sukiyra/sms-forwarder-board/code/globals.h

#ifndef GLOBALS_H
#define GLOBALS_H

#include <Arduino.h>
#include <WiFi.h>
#include <WiFiClientSecure.h>
#include <WebServer.h>
#include <Preferences.h>
#include <pdulib.h>
#define ENABLE_SMTP
#define ENABLE_DEBUG
#include <ReadyMail.h>
#include "config_types.h"

// 串口映射
#define TXD 3
#define RXD 4
#define MODEM_EN_PIN 5

// LED引脚定义（用于通过CI验证，给个假的）
#ifndef LED_BUILTIN
#define LED_BUILTIN 8
#endif

#define SERIAL_BUFFER_SIZE 500
#define MODEM_RX_BUFFER_SIZE 8192
#define MAX_PDU_LENGTH 300
#define FIRMWARE_VERSION "sukiyra-1.6.5"

// 全局变量声明
extern Config config;
extern Preferences preferences;
extern PDU pdu;
extern WiFiClientSecure ssl_client;
extern SMTPClient smtp;
extern WebServer server;
extern bool configValid;
extern bool modemReady;
extern String detectedModemManufacturer;
extern String detectedModemModel;
extern String detectedModemFirmware;
extern String detectedModemFamily;
extern unsigned long lastPrintTime;
extern ConcatSms concatBuffer[MAX_CONCAT_MESSAGES];

#endif
