sukiyra/sms-forwarder-board/code/web_handlers.h

#ifndef WEB_HANDLERS_H
#define WEB_HANDLERS_H

#include "globals.h"

#define LOG_BUF_SIZE 80
#define LOG_LINE_MAX_SIZE 320

extern String logBuffer[LOG_BUF_SIZE];
extern int logBufIdx;
extern int logBufCount;

void logCapture(const String& msg);
void logCapture(const char* msg);
void logCaptureF(const char* fmt, ...);
void logCaptureLn(const String& msg);
void logCaptureLn(const char* msg);

bool checkAuth();
void sendJsonResponse(int status, const String &json);
void handleRoot();
void handleQuery();
bool wifiConnectAll();
void wifiStartAp();
void wifiMaintenanceLoop();
bool wifiProvisioningMode();
bool wifiStartScan(String &message);
String wifiScanStatusJson();
bool wifiStartConnectionTest(const String &ssid, const String &pass, String &message);
String wifiConnectionTestJson();
void handleATCommand();
void handlePing();
void handleLog();
void handleModem();
void handleWifi();

#endif
