sukiyra/sms-forwarder-board/code/push.h

#ifndef PUSH_H
#define PUSH_H

#include "globals.h"

void sendEmailNotification(const char* subject, const char* body);
void sendSMSToServer(const char* sender, const char* message, const char* timestamp);
void sendToChannel(const PushChannel& channel, const char* sender, const char* message, const char* timestamp);
String urlEncode(const String& str);
String jsonEscape(const String& str);
String notificationDisplayTime(const char* timestamp);
String dingtalkSign(const String& secret, int64_t timestamp);
int64_t getUtcMillis();

#endif
