sukiyra/sms-forwarder-board/code/sim_manager.cpp

#include "sim_manager.h"

#include "esim_manager.h"
#include "globals.h"
#include "modem.h"
#include "operator_manager.h"
#include "sms_process.h"
#include "sim_policy.h"
#include "web_handlers.h"

namespace {

constexpr unsigned long DETECT_INTERVAL_READY_MS = 2000UL;
constexpr unsigned long DETECT_INTERVAL_RETRY_MS = 1000UL;
constexpr unsigned long DETECT_CONFIRM_MS = 350UL;
constexpr unsigned long ML307Y_ABSENT_CONFIRM_MS = 3000UL;
constexpr unsigned long COMMAND_TIMEOUT_MS = 2500UL;
constexpr unsigned long CGACT_TIMEOUT_MS = 5000UL;
constexpr unsigned long SIGNAL_INTERVAL_MS = 10000UL;
constexpr unsigned long SIGNAL_STALE_MS = 45000UL;
constexpr size_t RESPONSE_CAPACITY = 640;
constexpr uint8_t CONFIRMATION_COUNT = 2;

enum SimState {
  SIM_UNKNOWN,
  SIM_DETECTING,
  SIM_ABSENT,
  SIM_PIN_REQUIRED,
  SIM_PUK_REQUIRED,
  SIM_READY,
  SIM_ERROR
};

enum Observation {
  OBS_UNKNOWN,
  OBS_DETECTING,
  OBS_ABSENT,
  OBS_PIN_REQUIRED,
  OBS_PUK_REQUIRED,
  OBS_READY,
  OBS_ERROR
};

enum WireStage {
  WIRE_IDLE,
  WIRE_CPIN,
  WIRE_CMEE,
  WIRE_CGACT,
  WIRE_ICCID,
  WIRE_ICCID_CRSM,
  WIRE_CNUM,
  WIRE_CIMI,
  WIRE_CNMI,
  WIRE_CNMI_STORED,
  WIRE_CMGF,
  WIRE_CEREG_ENABLE,
  WIRE_CEREG_QUERY,
  WIRE_CEREG_PROBE,
  WIRE_CEREG_SIM_VERIFY,
  WIRE_CESQ
};

SimState state = SIM_UNKNOWN;
Observation candidate = OBS_UNKNOWN;
uint8_t candidateCount = 0;
WireStage wireStage = WIRE_IDLE;
bool known = false;
bool present = false;
bool smsReady = false;
bool needsConfigure = false;
bool ownsExclusive = false;
bool probeRegistrationNext = false;
uint8_t configAttempts = 0;
uint8_t transportFailures = 0;
uint8_t ml307yAbsentVerificationFailures = 0;
uint32_t generation = 0;
unsigned long changedAt = 0;
unsigned long nextActionAt = 0;
unsigned long commandStartedAt = 0;
unsigned long commandTimeout = COMMAND_TIMEOUT_MS;
char responseBuffer[RESPONSE_CAPACITY];
size_t responseLength = 0;
String activeIccidTail;
String activePhoneNumber;
String activeHomePlmn;
int activeRegistrationStatus = -1;
bool signalKnown = false;
bool signalRsrqKnown = false;
int signalRsrpDbm = 0;
int signalRsrqTenthsDb = 0;
bool startWire(const char* command, WireStage stage,
               unsigned long timeout = COMMAND_TIMEOUT_MS);
int signalRsrpRaw = -1;
int signalRsrqRaw = -1;
unsigned long signalUpdatedAt = 0;
unsigned long signalNextAt = 0;
unsigned long simErrorStartedAt = 0;
unsigned long configurationStartedAt = 0;
String stateDetail;

bool elapsed(unsigned long now, unsigned long deadline) {
  return static_cast<long>(now - deadline) >= 0;
}

const char* stateName(SimState value) {
  switch (value) {
    case SIM_DETECTING: return "detecting";
    case SIM_ABSENT: return "absent";
    case SIM_PIN_REQUIRED: return "pin_required";
    case SIM_PUK_REQUIRED: return "puk_required";
    case SIM_READY: return "ready";
    case SIM_ERROR: return "error";
    default: return "unknown";
  }
}

const char* stateMessage(SimState value) {
  switch (value) {
    case SIM_DETECTING:
      return stateDetail.length()
                 ? stateDetail.c_str()
                 : (present ? "SIM 已识别，正在恢复短信服务" : "正在检测 SIM 卡");
    case SIM_ABSENT: return "未检测到 SIM 卡";
    case SIM_PIN_REQUIRED: return "SIM 卡需要 PIN 解锁";
    case SIM_PUK_REQUIRED: return "SIM 卡需要 PUK 解锁";
    case SIM_READY: return smsReady ? "SIM 已就绪" : "SIM 已识别，短信服务尚未就绪";
    case SIM_ERROR:
      return stateDetail.length() ? stateDetail.c_str() : "SIM 卡持续返回硬件错误";
    default: return "SIM 状态尚未确认";
  }
}

void publishState(SimState next, bool nextKnown, bool nextPresent) {
  bool changed = state != next || known != nextKnown || present != nextPresent;
  state = next;
  known = nextKnown;
  present = nextPresent;
  if (!changed) return;
  ++generation;
  changedAt = millis();
  logCaptureLn(String("SIM 状态更新：") + stateMessage(state));
}

void releaseWire() {
  if (ownsExclusive) modemReleaseExclusive();
  ownsExclusive = false;
  wireStage = WIRE_IDLE;
  responseLength = 0;
  memset(responseBuffer, 0, sizeof(responseBuffer));
}

bool lineEquals(const char* expected) {
  size_t start = 0;
  while (start < responseLength) {
    size_t end = start;
    while (end < responseLength && responseBuffer[end] != '\n') ++end;
    while (start < end && (responseBuffer[start] == '\r' || responseBuffer[start] == ' ')) ++start;
    while (end > start && (responseBuffer[end - 1] == '\r' || responseBuffer[end - 1] == ' ')) --end;
    size_t expectedLength = strlen(expected);
    if (end - start == expectedLength &&
        memcmp(responseBuffer + start, expected, expectedLength) == 0) return true;
    start = end + 1;
  }
  return false;
}

bool responseHas(const char* value) {
  return strstr(responseBuffer, value) != nullptr;
}

bool responseError() {
  return lineEquals("ERROR") || responseHas("+CME ERROR:") || responseHas("+CMS ERROR:");
}

int cmeErrorCode() {
  const char* marker = strstr(responseBuffer, "+CME ERROR:");
  if (!marker) return -1;
  marker += strlen("+CME ERROR:");
  while (*marker == ' ') ++marker;
  if (*marker < '0' || *marker > '9') return -1;
  return atoi(marker);
}

Observation parseCpinObservation() {
  if (responseHas("+CPIN: READY")) return OBS_READY;
  if (responseHas("+CPIN: SIM PIN") || responseHas("SIM PIN required")) return OBS_PIN_REQUIRED;
  if (responseHas("+CPIN: SIM PUK") || responseHas("SIM PUK required")) return OBS_PUK_REQUIRED;
  int cme = cmeErrorCode();
  if (cme == 10 || responseHas("SIM not inserted")) return OBS_ABSENT;
  if (cme == 11) return OBS_PIN_REQUIRED;
  if (cme == 12) return OBS_PUK_REQUIRED;
  if (cme == 14 || cme == 512 || responseHas("SIM busy") || responseHas("SIM not ready")) {
    stateDetail = "SIM / eUICC 正在初始化，设备会自动重试";
    return OBS_DETECTING;
  }
  if (cme == 13 || cme == 15 || responseHas("SIM failure") || responseHas("SIM wrong")) {
    stateDetail = cme >= 0 ? "SIM / eUICC 暂时返回错误 " + String(cme) + "，正在等待恢复"
                           : "SIM / eUICC 暂时返回错误，正在等待恢复";
    return OBS_ERROR;
  }
  // SIM busy/not ready and a missing terminal response are transient. They must
  // never be promoted to a false card-removal event.
  return OBS_UNKNOWN;
}

int parseCeregStatus() {
  int queryStatus = -1;
  int urcStatus = -1;
  const char* search = responseBuffer;
  while (const char* marker = strstr(search, "+CEREG:")) {
    marker += strlen("+CEREG:");
    while (*marker == ' ') ++marker;
    char* end = nullptr;
    long first = strtol(marker, &end, 10);
    if (end != marker && first >= 0 && first <= 5) {
      while (*end == ' ') ++end;
      if (*end != ',') {
        urcStatus = static_cast<int>(first);
      } else {
        const char* secondStart = end + 1;
        while (*secondStart == ' ') ++secondStart;
        // Query responses are <n>,<stat>; extended unsolicited reports are
        // <stat>,"<tac>" and therefore have a quote after the first comma.
        if (*secondStart == '"') {
          urcStatus = static_cast<int>(first);
        } else {
          char* secondEnd = nullptr;
          long second = strtol(secondStart, &secondEnd, 10);
          if (secondEnd != secondStart && second >= 0 && second <= 5) {
            queryStatus = static_cast<int>(second);
          }
        }
      }
    }
    const char* lineEnd = strchr(marker, '\n');
    if (!lineEnd) break;
    search = lineEnd + 1;
  }
  return queryStatus >= 0 ? queryStatus : urcStatus;
}

String parseIccidTail(const char* response) {
  if (!response) return "";
  const char* marker = strstr(response, "+ICCID:");
  if (!marker) return "";
  marker += strlen("+ICCID:");
  const char* lineEnd = marker;
  while (*lineEnd && *lineEnd != '\r' && *lineEnd != '\n') ++lineEnd;
  while (marker < lineEnd && (*marker == ' ' || *marker == '\t')) ++marker;
  while (lineEnd > marker &&
         (lineEnd[-1] == ' ' || lineEnd[-1] == '\t')) --lineEnd;
  if (marker < lineEnd && *marker == '"') ++marker;
  if (lineEnd > marker && lineEnd[-1] == '"') --lineEnd;
  // ML307R may append the ISO/IEC 7816 filler nibble used for an odd-length
  // ICCID (for example 19 decimal digits followed by F).
  if (lineEnd > marker && (lineEnd[-1] == 'F' || lineEnd[-1] == 'f')) --lineEnd;
  const size_t length = static_cast<size_t>(lineEnd - marker);
  if (length < 18 || length > 22) return "";
  for (const char* p = marker; p < lineEnd; ++p) {
    if (!isDigit(*p)) return "";
  }
  String tail;
  tail.reserve(4);
  for (const char* p = lineEnd - 4; p < lineEnd; ++p) tail += *p;
  return tail;
}

String parseCrsmIccidTail(const char* response) {
  if (!response) return "";
  const char* marker = strstr(response, "+CRSM:");
  if (!marker) return "";
  marker = strchr(marker, '"');
  if (!marker) return "";
  ++marker;
  const char* end = strchr(marker, '"');
  if (!end || end - marker != 20) return "";

  String digits;
  digits.reserve(20);
  for (const char* p = marker; p < end; p += 2) {
    if (!isHexadecimalDigit(p[0]) || !isHexadecimalDigit(p[1])) return "";
    digits += p[1];
    digits += p[0];
  }
  if (digits.endsWith("F") || digits.endsWith("f")) digits.remove(digits.length() - 1);
  if (digits.length() < 18 || digits.length() > 20) return "";
  for (size_t i = 0; i < digits.length(); ++i) {
    if (!isDigit(digits[i])) return "";
  }
  return digits.substring(digits.length() - 4);
}

String parsePhoneNumber(const char* response) {
  if (!response) return "";
  const char* marker = strstr(response, "+CNUM:");
  if (!marker) return "";
  marker = strchr(marker, ',');
  if (!marker) return "";
  ++marker;
  while (*marker == ' ' || *marker == '\t') ++marker;

  const char* end = marker;
  if (*marker == '"') {
    ++marker;
    end = strchr(marker, '"');
  } else {
    while (*end && *end != ',' && *end != '\r' && *end != '\n') ++end;
  }
  if (!end || end <= marker) return "";

  String number;
  number.reserve(static_cast<size_t>(end - marker));
  for (const char* p = marker; p < end; ++p) {
    if (*p == '+' && p == marker) {
      number += *p;
    } else if (isDigit(*p)) {
      number += *p;
    } else if (*p != ' ' && *p != '-') {
      return "";
    }
  }
  size_t digits = number.startsWith("+") ? number.length() - 1 : number.length();
  return digits >= 3 && digits <= 20 ? number : "";
}

String parseHomePlmn(const char* response) {
  if (!response) return "";
  const char* line = response;
  while (*line) {
    while (*line == '\r' || *line == '\n' || *line == ' ' || *line == '\t') ++line;
    const char* end = line;
    while (*end && *end != '\r' && *end != '\n') ++end;
    const size_t length = static_cast<size_t>(end - line);
    if (length >= 14 && length <= 16) {
      bool allDigits = true;
      for (const char* p = line; p < end; ++p) {
        if (!isDigit(*p)) {
          allDigits = false;
          break;
        }
      }
      if (allDigits) {
        String plmn;
        plmn.reserve(5);
        for (uint8_t i = 0; i < 5; ++i) plmn += line[i];
        return plmn;
      }
    }
    line = end;
  }
  return "";
}

void clearSignalCache() {
  signalKnown = false;
  signalRsrqKnown = false;
  signalRsrpDbm = 0;
  signalRsrqTenthsDb = 0;
  signalRsrpRaw = -1;
  signalRsrqRaw = -1;
  signalUpdatedAt = 0;
  signalNextAt = millis();
}

bool updateSignalFromCesq() {
  const char* marker = strstr(responseBuffer, "+CESQ:");
  if (!marker) return false;
  int rxlev = 0;
  int ber = 0;
  int rscp = 0;
  int ecno = 0;
  int rsrq = 0;
  int rsrp = 0;
  if (sscanf(marker, "+CESQ: %d,%d,%d,%d,%d,%d",
             &rxlev, &ber, &rscp, &ecno, &rsrq, &rsrp) != 6) {
    return false;
  }

  signalRsrpRaw = rsrp;
  signalRsrqRaw = rsrq;
  signalKnown = rsrp >= 0 && rsrp <= 97;
  signalRsrqKnown = rsrq >= 0 && rsrq <= 34;
  if (signalKnown) signalRsrpDbm = -140 + rsrp;
  if (signalRsrqKnown) signalRsrqTenthsDb = -195 + rsrq * 5;
  signalUpdatedAt = millis();
  return true;
}

void invalidateCardCaches() {
  modemReady = false;
  smsReady = false;
  modemSetSmsDeliveryMode("unconfigured");
  probeRegistrationNext = false;
  activeIccidTail = "";
  activePhoneNumber = "";
  activeHomePlmn = "";
  activeRegistrationStatus = -1;
  clearSignalCache();
  esimManagerResetCapability();
  operatorManagerInvalidate();
  smsResetForSimChange();
}

void commitObservation(Observation observation) {
  candidate = OBS_UNKNOWN;
  candidateCount = 0;
  transportFailures = 0;

  switch (observation) {
    case OBS_DETECTING:
      needsConfigure = false;
      configAttempts = 0;
      modemReady = false;
      smsReady = false;
      publishState(SIM_DETECTING, true, true);
      nextActionAt = millis() + DETECT_INTERVAL_RETRY_MS;
      break;
    case OBS_ABSENT:
      stateDetail = "";
      needsConfigure = false;
      configAttempts = 0;
      if (state != SIM_ABSENT || present) invalidateCardCaches();
      publishState(SIM_ABSENT, true, false);
      nextActionAt = millis() + DETECT_INTERVAL_RETRY_MS;
      break;
    case OBS_PIN_REQUIRED:
      stateDetail = "";
      needsConfigure = false;
      configAttempts = 0;
      if (state != SIM_PIN_REQUIRED || !present) invalidateCardCaches();
      publishState(SIM_PIN_REQUIRED, true, true);
      nextActionAt = millis() + DETECT_INTERVAL_RETRY_MS;
      break;
    case OBS_PUK_REQUIRED:
      stateDetail = "";
      needsConfigure = false;
      configAttempts = 0;
      if (state != SIM_PUK_REQUIRED || !present) invalidateCardCaches();
      publishState(SIM_PUK_REQUIRED, true, true);
      nextActionAt = millis() + DETECT_INTERVAL_RETRY_MS;
      break;
    case OBS_ERROR:
      needsConfigure = false;
      configAttempts = 0;
      if (state != SIM_ERROR || !present) invalidateCardCaches();
      publishState(SIM_ERROR, true, true);
      nextActionAt = millis() + DETECT_INTERVAL_RETRY_MS;
      break;
    case OBS_READY: {
      simErrorStartedAt = 0;
      stateDetail = "";
      bool newlyReady = state != SIM_READY || !present || !smsReady;
      if (newlyReady) {
        modemReady = false;
        smsReady = false;
        esimManagerResetCapability();
        operatorManagerInvalidate();
        needsConfigure = true;
        configAttempts = 0;
        configurationStartedAt = millis();
        publishState(SIM_DETECTING, true, true);
        nextActionAt = millis();
      } else {
        nextActionAt = millis() + DETECT_INTERVAL_READY_MS;
      }
      break;
    }
    default:
      nextActionAt = millis() + DETECT_INTERVAL_RETRY_MS;
      break;
  }
}

void observe(Observation observation) {
  if (observation == OBS_ERROR) {
    unsigned long now = millis();
    if (!simErrorStartedAt) simErrorStartedAt = now;
    if (!simpolicy::hardwareErrorIsPersistent(now - simErrorStartedAt)) {
      candidate = OBS_UNKNOWN;
      candidateCount = 0;
      transportFailures = 0;
      if (state != SIM_READY) publishState(SIM_DETECTING, true, true);
      nextActionAt = now + DETECT_INTERVAL_RETRY_MS;
      return;
    }
    stateDetail = "SIM / eUICC 连续 30 秒返回硬件错误，请检查卡片接触或重启模组";
  } else if (observation == OBS_READY || observation == OBS_ABSENT ||
             observation == OBS_PIN_REQUIRED || observation == OBS_PUK_REQUIRED) {
    simErrorStartedAt = 0;
  }
  bool verifyMl307yAbsent = observation == OBS_ABSENT &&
                           detectedModemModel.startsWith("ML307Y");
  if (observation != OBS_ABSENT) ml307yAbsentVerificationFailures = 0;
  if (observation == OBS_UNKNOWN) {
    candidate = OBS_UNKNOWN;
    candidateCount = 0;
    if (++transportFailures >= 3 && state != SIM_ABSENT) {
      modemReady = false;
      smsReady = false;
      probeRegistrationNext = false;
      publishState(SIM_UNKNOWN, false, false);
    }
    nextActionAt = millis() + DETECT_INTERVAL_RETRY_MS;
    return;
  }

  bool matchesPublished =
      (observation == OBS_DETECTING && state == SIM_DETECTING && !needsConfigure) ||
      (observation == OBS_ABSENT && state == SIM_ABSENT) ||
      (observation == OBS_PIN_REQUIRED && state == SIM_PIN_REQUIRED) ||
      (observation == OBS_PUK_REQUIRED && state == SIM_PUK_REQUIRED) ||
      (observation == OBS_READY && state == SIM_READY && smsReady) ||
      (observation == OBS_ERROR && state == SIM_ERROR && !needsConfigure);
  if (matchesPublished) {
    candidate = OBS_UNKNOWN;
    candidateCount = 0;
    transportFailures = 0;
    probeRegistrationNext = observation == OBS_READY && !modemReady;
    nextActionAt = millis() + (probeRegistrationNext ? DETECT_INTERVAL_RETRY_MS
                                                      : (observation == OBS_READY
                                                             ? DETECT_INTERVAL_READY_MS
                                                             : DETECT_INTERVAL_RETRY_MS));
    return;
  }

  if (candidate != observation) {
    candidate = observation;
    candidateCount = 1;
    // A first definitive change immediately withdraws READY and invalidates
    // card-derived caches. The second sample still decides the final state,
    // but a quick remove/reinsert can no longer leave stale Profile data live.
    if (!verifyMl307yAbsent && state != SIM_UNKNOWN && state != SIM_DETECTING) {
      invalidateCardCaches();
      needsConfigure = false;
      configAttempts = 0;
      publishState(SIM_DETECTING, false, observation != OBS_ABSENT);
    }
  } else if (candidateCount < 255) {
    ++candidateCount;
  }
  if (candidateCount >= CONFIRMATION_COUNT) {
    // ML307Y can briefly (and sometimes persistently after COPS scans) return
    // CME 10 while it remains registered. Confirm that contradiction through
    // CEREG before withdrawing a working SIM and its SMS service.
    if (verifyMl307yAbsent) {
      if (!startWire("AT+CEREG?", WIRE_CEREG_SIM_VERIFY)) {
        nextActionAt = millis() + ML307Y_ABSENT_CONFIRM_MS;
      }
      return;
    }
    commitObservation(observation);
  } else {
    nextActionAt = millis() +
                   (verifyMl307yAbsent ? ML307Y_ABSENT_CONFIRM_MS : DETECT_CONFIRM_MS);
  }
}

bool startWire(const char* command, WireStage stage, unsigned long timeout) {
  if (wireStage != WIRE_IDLE || esimIsBusy() || operatorManagerIsBusy() ||
      smsReceiverAwaitingPdu()) return false;
  if (!modemAcquireExclusive()) return false;
  ownsExclusive = true;
  // Drain complete URCs before starting a transaction. If a +CMT header was
  // observed without its PDU, release the modem and let the PDU finish first.
  checkSerial1URC();
  if (smsReceiverAwaitingPdu()) {
    releaseWire();
    nextActionAt = millis() + 100;
    return false;
  }
  responseLength = 0;
  responseBuffer[0] = '\0';
  wireStage = stage;
  commandStartedAt = millis();
  commandTimeout = timeout;
  Serial1.println(command);
  return true;
}

const char* wireStageName(WireStage stage) {
  switch (stage) {
    case WIRE_CMEE: return "错误码设置";
    case WIRE_CGACT: return "数据通道关闭";
    case WIRE_ICCID: return "ICCID 读取";
    case WIRE_ICCID_CRSM: return "ICCID 兼容读取";
    case WIRE_CNUM: return "号码读取";
    case WIRE_CIMI: return "归属网络读取";
    case WIRE_CMGF: return "短信 PDU 模式";
    case WIRE_CNMI:
    case WIRE_CNMI_STORED: return "短信上报配置";
    case WIRE_CEREG_ENABLE:
    case WIRE_CEREG_QUERY: return "网络注册读取";
    default: return "SIM 初始化";
  }
}

void scheduleConfigurationRetry(WireStage failedStage) {
  smsReady = false;
  modemSetSmsDeliveryMode("unconfigured");
  needsConfigure = true;
  if (configAttempts < 255) ++configAttempts;
  if (!configurationStartedAt) configurationStartedAt = millis();
  stateDetail = String("SIM 已识别，正在重试") + wireStageName(failedStage) +
                "（第 " + String(configAttempts) + " 次）";
  if (simpolicy::configurationErrorIsPersistent(millis() - configurationStartedAt)) {
    stateDetail = String("SIM 已识别，但") + wireStageName(failedStage) +
                  "持续失败；设备仍会自动重试";
    publishState(SIM_ERROR, true, true);
  } else {
    publishState(SIM_DETECTING, true, true);
  }
  unsigned long retryDelay = 1000UL * (configAttempts ? configAttempts : 1);
  if (retryDelay > 5000UL) retryDelay = 5000UL;
  nextActionAt = millis() + retryDelay;
}

void handleWireResult(WireStage completed, bool ok) {
  if (completed == WIRE_CPIN) {
    Observation observation = parseCpinObservation();
    releaseWire();
    observe(observation);
    return;
  }

  if (completed == WIRE_CEREG_SIM_VERIFY) {
    int registration = ok ? parseCeregStatus() : -1;
    releaseWire();
    if (registration >= 0) activeRegistrationStatus = registration;
    if (registration == 1 || registration == 5) {
      bool wasReady = state == SIM_READY && smsReady;
      candidate = OBS_UNKNOWN;
      candidateCount = 0;
      ml307yAbsentVerificationFailures = 0;
      transportFailures = 0;
      modemReady = true;
      if (wasReady) {
        nextActionAt = millis() + DETECT_INTERVAL_READY_MS;
      } else {
        logCaptureLn("ML307Y CPIN 报未插卡，但蜂窝仍已注册；按在卡状态恢复短信服务");
        needsConfigure = true;
        configAttempts = 0;
        publishState(SIM_DETECTING, true, true);
        nextActionAt = millis();
      }
      return;
    }
    candidate = OBS_UNKNOWN;
    candidateCount = 0;
    if (registration >= 0 && ++ml307yAbsentVerificationFailures >= 3) {
      commitObservation(OBS_ABSENT);
    } else {
      nextActionAt = millis() + ML307Y_ABSENT_CONFIRM_MS;
    }
    return;
  }

  if (completed == WIRE_CEREG_PROBE) {
    int registration = ok ? parseCeregStatus() : -1;
    releaseWire();
    if (registration >= 0) {
      activeRegistrationStatus = registration;
      modemReady = registration == 1 || registration == 5;
    }
    if (modemReady) signalNextAt = millis();
    probeRegistrationNext = false;
    nextActionAt = millis() + DETECT_INTERVAL_READY_MS;
    return;
  }

  if (completed == WIRE_CESQ) {
    bool parsed = ok && updateSignalFromCesq();
    releaseWire();
    if (ok && !parsed) {
      signalKnown = false;
      signalRsrqKnown = false;
    }
    signalNextAt = millis() + SIGNAL_INTERVAL_MS;
    return;
  }

  if (!ok) {
    Observation observation = parseCpinObservation();
    releaseWire();
    if (observation == OBS_ABSENT || observation == OBS_PIN_REQUIRED ||
        observation == OBS_PUK_REQUIRED) {
      // A configuration command can reveal a card-state change, but still use
      // the normal two-sample debounce before publishing it.
      needsConfigure = false;
      observe(observation);
    } else if (completed == WIRE_CGACT) {
      // Disabling the PDP context is a safety best effort. SMS reception does
      // not depend on it, so continue restoring the mandatory settings.
      startWire("AT+ICCID", WIRE_ICCID);
    } else if (completed == WIRE_ICCID) {
      // ICCID is receiver metadata only. Never block SMS recovery when a
      // modem temporarily refuses this optional query.
      activeIccidTail = "";
      startWire("AT+CRSM=176,12258,0,0,10,,\"3F00\"", WIRE_ICCID_CRSM);
    } else if (completed == WIRE_ICCID_CRSM) {
      activeIccidTail = "";
      startWire("AT+CNUM", WIRE_CNUM);
    } else if (completed == WIRE_CNUM) {
      // Many operators do not provision MSISDN on the SIM. Treat an empty or
      // unsupported CNUM response as normal and continue SMS configuration.
      activePhoneNumber = "";
      startWire("AT+CIMI", WIRE_CIMI);
    } else if (completed == WIRE_CIMI) {
      activeHomePlmn = "";
      startWire("AT+CMGF=0", WIRE_CMGF);
    } else if (completed == WIRE_CNMI) {
      startWire("AT+CNMI=2,1,0,0,0", WIRE_CNMI_STORED);
    } else if (completed == WIRE_CMEE) {
      // During insertion recovery CMEE is best effort and configuration may
      // continue. During ordinary detection, retry CMEE later so a modem that
      // currently returns bare ERROR can recover numeric SIM diagnostics.
      if (needsConfigure) {
        if (modemSupportsPdpContextControl()) {
          startWire("AT+CGACT=0,1", WIRE_CGACT, CGACT_TIMEOUT_MS);
        } else {
          startWire("AT+ICCID", WIRE_ICCID);
        }
      } else {
        nextActionAt = millis() + DETECT_INTERVAL_RETRY_MS;
      }
    } else {
      scheduleConfigurationRetry(completed);
    }
    return;
  }

  int registration = completed == WIRE_CEREG_QUERY ? parseCeregStatus() : -1;
  String iccidTail = completed == WIRE_ICCID ? parseIccidTail(responseBuffer) : "";
  String crsmIccidTail = completed == WIRE_ICCID_CRSM ? parseCrsmIccidTail(responseBuffer) : "";
  String phoneNumber = completed == WIRE_CNUM ? parsePhoneNumber(responseBuffer) : "";
  String homePlmn = completed == WIRE_CIMI ? parseHomePlmn(responseBuffer) : "";
  releaseWire();
  switch (completed) {
    case WIRE_CMEE:
      if (needsConfigure) {
        if (modemSupportsPdpContextControl()) {
          startWire("AT+CGACT=0,1", WIRE_CGACT, CGACT_TIMEOUT_MS);
        } else {
          startWire("AT+ICCID", WIRE_ICCID);
        }
      } else {
        transportFailures = 0;
        nextActionAt = millis();
      }
      break;
    case WIRE_CGACT:
      startWire("AT+ICCID", WIRE_ICCID);
      break;
    case WIRE_ICCID:
      activeIccidTail = iccidTail;
      if (!activeIccidTail.length()) {
        startWire("AT+CRSM=176,12258,0,0,10,,\"3F00\"", WIRE_ICCID_CRSM);
        break;
      }
      startWire("AT+CNUM", WIRE_CNUM);
      break;
    case WIRE_ICCID_CRSM:
      activeIccidTail = crsmIccidTail;
      startWire("AT+CNUM", WIRE_CNUM);
      break;
    case WIRE_CNUM:
      activePhoneNumber = phoneNumber;
      startWire("AT+CIMI", WIRE_CIMI);
      break;
    case WIRE_CIMI:
      activeHomePlmn = homePlmn;
      startWire("AT+CMGF=0", WIRE_CMGF);
      break;
    case WIRE_CMGF:
      startWire("AT+CNMI=2,2,0,0,0", WIRE_CNMI);
      break;
    case WIRE_CNMI:
      modemSetSmsDeliveryMode("direct");
      startWire("AT+CEREG=2", WIRE_CEREG_ENABLE);
      break;
    case WIRE_CNMI_STORED:
      modemSetSmsDeliveryMode("stored");
      startWire("AT+CEREG=2", WIRE_CEREG_ENABLE);
      break;
    case WIRE_CEREG_ENABLE:
      startWire("AT+CEREG?", WIRE_CEREG_QUERY);
      break;
    case WIRE_CEREG_QUERY: {
      activeRegistrationStatus = registration;
      modemReady = registration == 1 || registration == 5;
      probeRegistrationNext = false;
      smsReady = true;
      needsConfigure = false;
      configAttempts = 0;
      configurationStartedAt = 0;
      stateDetail = "";
      publishState(SIM_READY, true, true);
      smsScanStoredMessages("SM", 50);
      signalNextAt = millis();
      nextActionAt = millis() + DETECT_INTERVAL_READY_MS;
      break;
    }
    default: break;
  }
}

void drainWire() {
  while (Serial1.available()) {
    char value = static_cast<char>(Serial1.read());
    dispatchSerial1Byte(value, false);
    if (responseLength + 1 < RESPONSE_CAPACITY) {
      responseBuffer[responseLength++] = value;
      responseBuffer[responseLength] = '\0';
    } else {
      WireStage completed = wireStage;
      releaseWire();
      if (completed == WIRE_CPIN) {
        observe(OBS_UNKNOWN);
      } else if (completed == WIRE_CEREG_PROBE) {
        probeRegistrationNext = false;
        nextActionAt = millis() + DETECT_INTERVAL_READY_MS;
      } else if (completed == WIRE_CESQ) {
        signalNextAt = millis() + SIGNAL_INTERVAL_MS;
      } else if (completed == WIRE_CEREG_SIM_VERIFY) {
        candidate = OBS_UNKNOWN;
        candidateCount = 0;
        nextActionAt = millis() + ML307Y_ABSENT_CONFIRM_MS;
      } else if (completed == WIRE_CGACT) {
        startWire("AT+ICCID", WIRE_ICCID);
      } else if (completed == WIRE_ICCID) {
        activeIccidTail = "";
        startWire("AT+CRSM=176,12258,0,0,10,,\"3F00\"", WIRE_ICCID_CRSM);
      } else if (completed == WIRE_ICCID_CRSM) {
        activeIccidTail = "";
        startWire("AT+CNUM", WIRE_CNUM);
      } else if (completed == WIRE_CNUM) {
        activePhoneNumber = "";
        startWire("AT+CIMI", WIRE_CIMI);
      } else if (completed == WIRE_CIMI) {
        activeHomePlmn = "";
        startWire("AT+CMGF=0", WIRE_CMGF);
      } else if (completed == WIRE_CNMI) {
        startWire("AT+CNMI=2,1,0,0,0", WIRE_CNMI_STORED);
      } else if (completed == WIRE_CMEE && !needsConfigure) {
        nextActionAt = millis() + DETECT_INTERVAL_RETRY_MS;
      } else {
        scheduleConfigurationRetry(completed);
      }
      return;
    }
  }

  if (lineEquals("OK") || responseError()) {
    WireStage completed = wireStage;
    handleWireResult(completed, lineEquals("OK") && !responseError());
    return;
  }
  if (millis() - commandStartedAt >= commandTimeout) {
    WireStage completed = wireStage;
    releaseWire();
    if (completed == WIRE_CPIN) {
      observe(OBS_UNKNOWN);
    } else if (completed == WIRE_CEREG_PROBE) {
      probeRegistrationNext = false;
      nextActionAt = millis() + DETECT_INTERVAL_READY_MS;
    } else if (completed == WIRE_CESQ) {
      signalNextAt = millis() + SIGNAL_INTERVAL_MS;
    } else if (completed == WIRE_CEREG_SIM_VERIFY) {
      candidate = OBS_UNKNOWN;
      candidateCount = 0;
      nextActionAt = millis() + ML307Y_ABSENT_CONFIRM_MS;
    } else if (completed == WIRE_CGACT) {
      startWire("AT+ICCID", WIRE_ICCID);
    } else if (completed == WIRE_ICCID) {
      activeIccidTail = "";
      startWire("AT+CRSM=176,12258,0,0,10,,\"3F00\"", WIRE_ICCID_CRSM);
    } else if (completed == WIRE_ICCID_CRSM) {
      activeIccidTail = "";
      startWire("AT+CNUM", WIRE_CNUM);
    } else if (completed == WIRE_CNUM) {
      activePhoneNumber = "";
      startWire("AT+CIMI", WIRE_CIMI);
    } else if (completed == WIRE_CIMI) {
      activeHomePlmn = "";
      startWire("AT+CMGF=0", WIRE_CMGF);
    } else if (completed == WIRE_CNMI) {
      startWire("AT+CNMI=2,1,0,0,0", WIRE_CNMI_STORED);
    } else if (completed == WIRE_CMEE && !needsConfigure) {
      nextActionAt = millis() + DETECT_INTERVAL_RETRY_MS;
    } else {
      scheduleConfigurationRetry(completed);
    }
  }
}

}  // namespace

void simManagerBegin() {
  state = SIM_UNKNOWN;
  candidate = OBS_UNKNOWN;
  candidateCount = 0;
  wireStage = WIRE_IDLE;
  known = false;
  present = false;
  smsReady = false;
  needsConfigure = false;
  ownsExclusive = false;
  probeRegistrationNext = false;
  configAttempts = 0;
  transportFailures = 0;
  ml307yAbsentVerificationFailures = 0;
  simErrorStartedAt = 0;
  configurationStartedAt = 0;
  stateDetail = "";
  modemReady = false;
  activeIccidTail = "";
  activePhoneNumber = "";
  activeHomePlmn = "";
  activeRegistrationStatus = -1;
  clearSignalCache();
  generation = 1;
  changedAt = millis();
  nextActionAt = millis();
}

void simManagerInvalidate() {
  if (wireStage != WIRE_IDLE) releaseWire();
  candidate = OBS_UNKNOWN;
  candidateCount = 0;
  transportFailures = 0;
  ml307yAbsentVerificationFailures = 0;
  needsConfigure = false;
  configAttempts = 0;
  simErrorStartedAt = 0;
  configurationStartedAt = 0;
  stateDetail = "正在重新识别 SIM / eUICC";
  invalidateCardCaches();
  publishState(SIM_DETECTING, false, false);
  nextActionAt = millis();
}

void simManagerRestoreSmsConfiguration() {
  if (!known || !present || state == SIM_PIN_REQUIRED || state == SIM_PUK_REQUIRED ||
      state == SIM_ABSENT) {
    return;
  }
  // Some ML307 firmware resets CMGF/CNMI while scanning or changing PLMN. Re-run the
  // normal card configuration chain without discarding the operator scan cache.
  smsReady = false;
  modemSetSmsDeliveryMode("unconfigured");
  needsConfigure = true;
  configAttempts = 0;
  configurationStartedAt = millis();
  stateDetail = "SIM 已识别，正在恢复短信服务";
  nextActionAt = millis();
  logCaptureLn("运营商操作结束，正在恢复短信 PDU 与上报配置");
}

void simManagerLoop() {
  if (wireStage != WIRE_IDLE) {
    drainWire();
    return;
  }
  if (esimIsBusy() || operatorManagerIsBusy() || modemIsBooting()) return;
  unsigned long now = millis();
  bool signalDue = state == SIM_READY && smsReady && elapsed(now, signalNextAt);
  if (!elapsed(now, nextActionAt) && !signalDue) return;

  if (needsConfigure) {
    // Numeric CME errors make an absent card unambiguous on subsequent probes.
    // The remaining configuration stages stay asynchronous and keep HTTP live.
    startWire("AT+CMEE=1", WIRE_CMEE);
    return;
  }
  if (transportFailures >= 3) {
    startWire("AT+CMEE=1", WIRE_CMEE);
    return;
  }
  if (state == SIM_READY && smsReady && !modemReady && probeRegistrationNext) {
    if (startWire("AT+CEREG?", WIRE_CEREG_PROBE)) probeRegistrationNext = false;
    return;
  }
  if (signalDue) {
    if (startWire("AT+CESQ", WIRE_CESQ)) signalNextAt = now + SIGNAL_INTERVAL_MS;
    return;
  }
  startWire("AT+CPIN?", WIRE_CPIN);
}

bool simManagerIsBusy() {
  return wireStage != WIRE_IDLE || ownsExclusive;
}

bool simManagerIsKnown() {
  return known;
}

bool simManagerIsPresent() {
  return present;
}

bool simManagerIsReady() {
  return state == SIM_READY && known && present;
}

bool simManagerSmsReady() {
  return smsReady;
}

String simManagerIccidTail() {
  return activeIccidTail;
}

String simManagerPhoneNumber() {
  return activePhoneNumber;
}

String simManagerHomePlmn() {
  return activeHomePlmn;
}

int simManagerRegistrationStatus() {
  return activeRegistrationStatus;
}

bool simManagerIsRoaming() {
  return activeRegistrationStatus == 5;
}

void simManagerCaptureIccid(const String &response) {
  activeIccidTail = parseIccidTail(response.c_str());
}

bool simManagerSignalKnown() {
  return signalKnown && signalUpdatedAt && millis() - signalUpdatedAt <= SIGNAL_STALE_MS;
}

bool simManagerSignalRsrqKnown() {
  return simManagerSignalKnown() && signalRsrqKnown;
}

int simManagerSignalRsrpDbm() {
  return signalRsrpDbm;
}

int simManagerSignalRsrqTenthsDb() {
  return signalRsrqTenthsDb;
}

int simManagerSignalRsrpRaw() {
  return signalRsrpRaw;
}

unsigned long simManagerSignalUpdatedAt() {
  return signalUpdatedAt;
}

const char* simManagerStateName() {
  return stateName(state);
}

const char* simManagerMessage() {
  return stateMessage(state);
}

uint32_t simManagerGeneration() {
  return generation;
}

unsigned long simManagerChangedAt() {
  return changedAt;
}
